ULINKSZ/meshtastic/Software/firmware-master/src/platform/nrf52/architecture.h

#pragma once

#define ARCH_NRF52

//
// defaults for NRF52 architecture
//
#ifndef HAS_BLUETOOTH
#define HAS_BLUETOOTH 1
#endif
#ifndef HAS_SCREEN
#define HAS_SCREEN 1
#endif
#ifndef HAS_WIRE
#define HAS_WIRE 1
#endif
#ifndef HAS_GPS
#define HAS_GPS 1
#endif
#ifndef HAS_BUTTON
#define HAS_BUTTON 1
#endif
#ifndef HAS_TELEMETRY
#define HAS_TELEMETRY 1
#endif
#ifndef HAS_SENSOR
#define HAS_SENSOR 0
#endif
#ifndef HAS_RADIO
#define HAS_RADIO 1
#endif
#ifndef HAS_CPU_SHUTDOWN
#define HAS_CPU_SHUTDOWN 1
#endif

//
// set HW_VENDOR
//

// This string must exactly match the case used in release file names or the android updater won't work
#ifdef ARDUINO_NRF52840_PCA10056
#define HW_VENDOR meshtastic_HardwareModel_NRF52840DK
#elif defined(ARDUINO_NRF52840_PPR)
#define HW_VENDOR meshtastic_HardwareModel_PPR
#elif defined(RAK2560)
#define HW_VENDOR meshtastic_HardwareModel_RAK2560
#elif defined(RAK4630)
#define HW_VENDOR meshtastic_HardwareModel_RAK4631
#elif defined(TTGO_T_ECHO)
#define HW_VENDOR meshtastic_HardwareModel_T_ECHO
#elif defined(NANO_G2_ULTRA)
#define HW_VENDOR meshtastic_HardwareModel_NANO_G2_ULTRA
#elif defined(CANARYONE)
#define HW_VENDOR meshtastic_HardwareModel_CANARYONE
#elif defined(NORDIC_PCA10059)
#define HW_VENDOR meshtastic_HardwareModel_NRF52840_PCA10059
#elif defined(TWC_MESH_V4)
#define HW_VENDOR meshtastic_HardwareModel_TWC_MESH_V4
#elif defined(NRF52_PROMICRO_DIY)
#define HW_VENDOR meshtastic_HardwareModel_NRF52_PROMICRO_DIY
#elif defined(WIO_WM1110)
#define HW_VENDOR meshtastic_HardwareModel_WIO_WM1110
#elif defined(TRACKER_T1000_E)
#define HW_VENDOR meshtastic_HardwareModel_TRACKER_T1000_E
#elif defined(PRIVATE_HW) || defined(FEATHER_DIY)
#define HW_VENDOR meshtastic_HardwareModel_PRIVATE_HW
#else
#define HW_VENDOR meshtastic_HardwareModel_NRF52_UNKNOWN
#endif

//
// Standard definitions for NRF52 targets
//

#ifdef ARDUINO_NRF52840_PCA10056

// This board uses 0 to be mean LED on
#undef LED_INVERTED
#define LED_INVERTED 1

#endif

#ifdef _SEEED_XIAO_NRF52840_SENSE_H_

// This board uses 0 to be mean LED on
#undef LED_INVERTED
#define LED_INVERTED 1

#endif

#ifndef TTGO_T_ECHO
#define GPS_UBLOX
#endif

#define LED_PIN PIN_LED1 // LED1 on nrf52840-DK

#ifdef PIN_BUTTON1
#define BUTTON_PIN PIN_BUTTON1
#endif

#ifdef PIN_BUTTON2
#define BUTTON_PIN_ALT PIN_BUTTON2
#endif

#ifdef PIN_BUTTON_TOUCH
#define BUTTON_PIN_TOUCH PIN_BUTTON_TOUCH
#endif

#ifndef HAS_MAX17048
#define HAS_PMU
#define HAS_MAX17048 1
#endif

// Always include the SEGGER code on NRF52 - because useful for debugging
#include "SEGGER_RTT.h"

// The channel we send stdout data to
#define SEGGER_STDOUT_CH 0

// Debug printing to segger console
#define SEGGER_MSG(...) SEGGER_RTT_printf(SEGGER_STDOUT_CH, __VA_ARGS__)

// If we are not on a NRF52840 (which has built in USB-ACM serial support) and we don't have serial pins hooked up, then we MUST
// use SEGGER for debug output
// #define USE_SEGGER
#if !defined(PIN_SERIAL_RX) && !defined(NRF52840_XXAA)
// No serial ports on this board - ONLY use segger in memory console
#define USE_SEGGER
#endif
